jbobrow/AutomaTiles/Arduino/AutomaTiles/avr/cores/AutomaTiles/Arduino.h

/*
  Arduino.h - Main include file for the Arduino SDK
  Copyright (c) 2005-2013 Arduino Team.  All right reserved.

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
  You should have received a copy of the GNU Lesser General Public
  License along with this library; if not, write to the Free Software
  Foundation, Inc., 51 Franklin St, Fifth Floor, Boston, MA  02110-1301  USA
*/

#ifndef Arduino_h
#define Arduino_h

#include <stdlib.h>
#include <stdbool.h>
#include <string.h>
#include <math.h>

#include <avr/pgmspace.h>
#include <avr/io.h>
#include <avr/interrupt.h>

#include "binary.h"
//#include "AutomaTiles.h"

#ifdef __cplusplus
extern "C"{
#endif

void yield(void);

#define HIGH 0x1
#define LOW  0x0

#define INPUT 0x0
#define OUTPUT 0x1
#define INPUT_PULLUP 0x2

#define PI 3.1415926535897932384626433832795
#define HALF_PI 1.5707963267948966192313216916398
#define TWO_PI 6.283185307179586476925286766559
#define DEG_TO_RAD 0.017453292519943295769236907684886
#define RAD_TO_DEG 57.295779513082320876798154814105
#define EULER 2.718281828459045235360287471352

#define SERIAL  0x0
#define DISPLAY 0x1

#define LSBFIRST 0
#define MSBFIRST 1

#define CHANGE 1
#define FALLING 2
#define RISING 3

#define DEFAULT 0
#define EXTERNAL 1
#define INTERNAL 2

// undefine stdlib's abs if encountered
#ifdef abs
#undef abs
#endif

#define min(a,b) ((a)<(b)?(a):(b))
#define max(a,b) ((a)>(b)?(a):(b))
#define abs(x) ((x)>0?(x):-(x))
#define constrain(amt,low,high) ((amt)<(low)?(low):((amt)>(high)?(high):(amt)))
#define round(x)     ((x)>=0?(long)((x)+0.5):(long)((x)-0.5))
#define radians(deg) ((deg)*DEG_TO_RAD)
#define degrees(rad) ((rad)*RAD_TO_DEG)
#define sq(x) ((x)*(x))

#define interrupts() sei()
#define noInterrupts() cli()

#define clockCyclesPerMicrosecond() ( F_CPU / 1000000L )
#define clockCyclesToMicroseconds(a) ( (a) / clockCyclesPerMicrosecond() )
#define microsecondsToClockCycles(a) ( (a) * clockCyclesPerMicrosecond() )

#define lowByte(w) ((uint8_t) ((w) & 0xff))
#define highByte(w) ((uint8_t) ((w) >> 8))

#define bitRead(value, bit) (((value) >> (bit)) & 0x01)
#define bitSet(value, bit) ((value) |= (1UL << (bit)))
#define bitClear(value, bit) ((value) &= ~(1UL << (bit)))
#define bitWrite(value, bit, bitvalue) (bitvalue ? bitSet(value, bit) : bitClear(value, bit))

// avr-libc defines _NOP() since 1.6.2
#ifndef _NOP
#define _NOP() do { __asm__ volatile ("nop"); } while (0)
#endif

typedef unsigned int word;

#define bit(b) (1UL << (b))

typedef bool boolean;
typedef uint8_t byte;

void init(void);
void initVariant(void);

int atexit(void (*func)()) __attribute__((weak));

//void pinMode(uint8_t, uint8_t);
//void digitalWrite(uint8_t, uint8_t);
//int digitalRead(uint8_t);
//int analogRead(uint8_t);
//void analogReference(uint8_t mode);
//void analogWrite(uint8_t, int);

//unsigned long millis(void);
//unsigned long micros(void);
//void delay(unsigned long);
//void delayMicroseconds(unsigned int us);
//unsigned long pulseIn(uint8_t pin, uint8_t state, unsigned long timeout);

//void shiftOut(uint8_t dataPin, uint8_t clockPin, uint8_t bitOrder, uint8_t val);
//uint8_t shiftIn(uint8_t dataPin, uint8_t clockPin, uint8_t bitOrder);

//void attachInterrupt(uint8_t, void (*)(void), int mode);
//void detachInterrupt(uint8_t);
typedef void (*cb_func)(void);

void tileSetup(void);
void getNeighborStates(uint8_t * result);
void sendStep(void);
uint32_t getTimer(void);
void setColor(const uint8_t color[3]);
void setState(uint8_t state);
uint8_t getState(void);
void setStepCallback(cb_func cb);
void setButtonCallback(cb_func cb);
void setLongButtonCallback(cb_func cb, uint16_t ms);
void setLongButtonCallbackTimer(uint16_t ms);
void setTimerCallback(cb_func cb, uint16_t ms);
void setTimerCallbackTime(uint16_t ms);
void setTimeout(uint16_t seconds);
void setMicOn();
void setMicOff();
void setSharedDataBuffer(volatile uint8_t* comb,volatile uint8_t* datb , uint8_t len);
uint8_t getSharedData(uint8_t i);

enum MODE
{
	sleep,
	running,
	recieving,
	transmitting
};

extern enum MODE mode;

extern uint32_t timeout;
extern volatile uint32_t sleepTimer;

void setup(void);
void loop(void);

// Get the bit location within the hardware port of the given virtual pin.
// This comes from the pins_*.c file for the active board configuration.

#define analogInPinToBit(P) (P)

// Get the bit location within the hardware port of the given virtual pin.
// This comes from the pins_*.c file for the active board configuration.
// 
// These perform slightly better as macros compared to inline functions
//
#define digitalPinToPort(P) ( pgm_read_byte( digital_pin_to_port_PGM + (P) ) )
#define digitalPinToBitMask(P) ( pgm_read_byte( digital_pin_to_bit_mask_PGM + (P) ) )
#define digitalPinToTimer(P) ( pgm_read_byte( digital_pin_to_timer_PGM + (P) ) )
#define analogInPinToBit(P) (P)
#define portOutputRegister(P) ( (volatile uint8_t *)( pgm_read_word( port_to_output_PGM + (P))) )
#define portInputRegister(P) ( (volatile uint8_t *)( pgm_read_word( port_to_input_PGM + (P))) )
#define portModeRegister(P) ( (volatile uint8_t *)( pgm_read_word( port_to_mode_PGM + (P))) )

#define NOT_A_PIN 0
#define NOT_A_PORT 0

#define NOT_AN_INTERRUPT -1

#ifdef ARDUINO_MAIN
#define PA 1
#define PB 2
#define PC 3
#define PD 4
#define PE 5
#define PF 6
#define PG 7
#define PH 8
#define PJ 10
#define PK 11
#define PL 12
#endif

#define NOT_ON_TIMER 0
#define TIMER0A 1
#define TIMER0B 2
#define TIMER1A 3
#define TIMER1B 4
#define TIMER1C 5
#define TIMER2  6
#define TIMER2A 7
#define TIMER2B 8

#define TIMER3A 9
#define TIMER3B 10
#define TIMER3C 11
#define TIMER4A 12
#define TIMER4B 13
#define TIMER4C 14
#define TIMER4D 15
#define TIMER5A 16
#define TIMER5B 17
#define TIMER5C 18

#ifdef __cplusplus
} // extern "C"
#endif

#ifdef __cplusplus
#include "WCharacter.h"
#include "WString.h"
#if defined(HAVE_HWSERIAL0) && defined(HAVE_CDCSERIAL)
#error "Targets with both UART0 and CDC serial not supported"
#endif

uint16_t makeWord(uint16_t w);
uint16_t makeWord(byte h, byte l);

#define word(...) makeWord(__VA_ARGS__)

//unsigned long pulseIn(uint8_t pin, uint8_t state, unsigned long timeout = 1000000L);

//void tone(uint8_t _pin, unsigned int frequency, unsigned long duration = 0);
//void noTone(uint8_t _pin);


// WMath prototypes
long random(long);
long random(long, long);
void randomSeed(unsigned int);
long map(long, long, long, long, long);

#endif

#include "Pins.h"

#endif
